Macartney-Christopher/5-Axis-Camera-Position-Control/Step Files/Focus & Zoom Extension/Small Lens Double Motor Platform.STEP

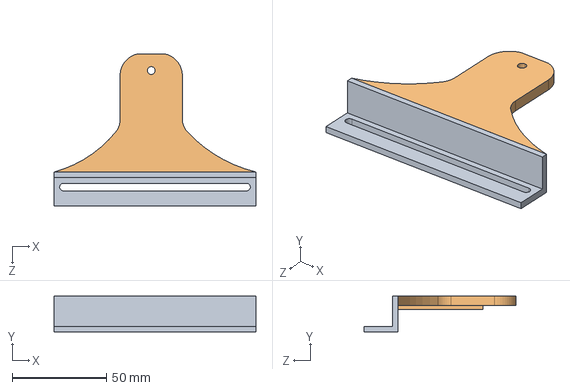
[picture p15: CAD file, 2021-04-19]
Step Files/Focus & Zoom Extension/Small Lens Double Motor Platform.STEP
107.0 x 19.0 x 80.5 mm
