Macartney-Christopher/5-Axis-Camera-Position-Control/Step Files/Tilt Hall Effect and Stepper Mount.STEP

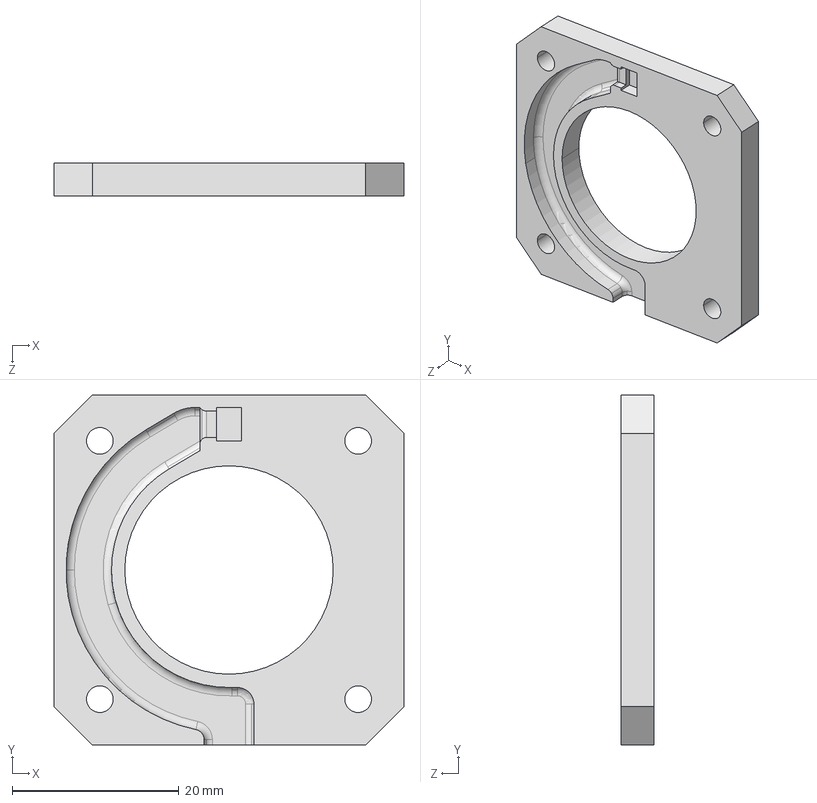
[picture p16: CAD file, 2021-03-15]
Step Files/Tilt Hall Effect and Stepper Mount.STEP
42.0 x 42.0 x 4.00 mm
