Macartney-Christopher/5-Axis-Camera-Position-Control/Step Files/Belt Clamp Lever.STEP

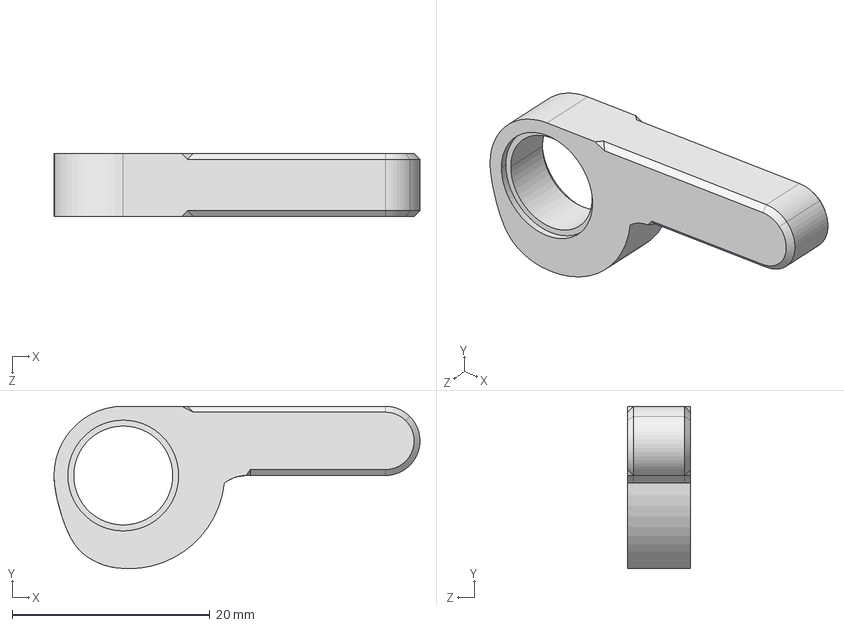
[picture p17: CAD file, 2021-03-15]
Step Files/Belt Clamp Lever.STEP
37.0 x 16.4 x 6.40 mm
