Macartney-Christopher/5-Axis-Camera-Position-Control/Step Files/Dynamic Lighting/Tripod Mount.STEP

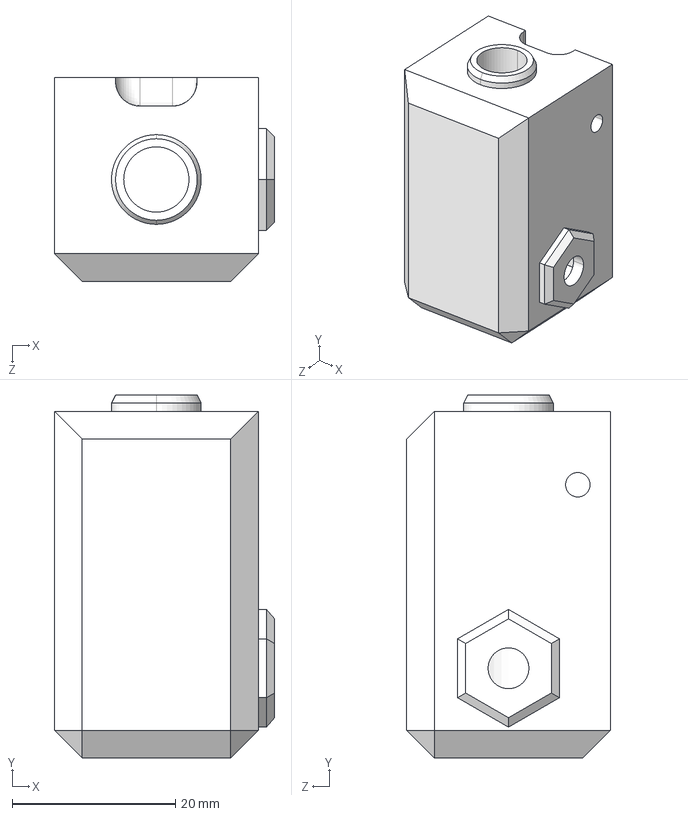
[picture p18: CAD file, 2021-04-19]
Step Files/Dynamic Lighting/Tripod Mount.STEP
27.0 x 44.5 x 25.0 mm
