Macartney-Christopher/5-Axis-Camera-Position-Control/Step Files/Focus & Zoom Extension/Tilt Camera Mount.STEP

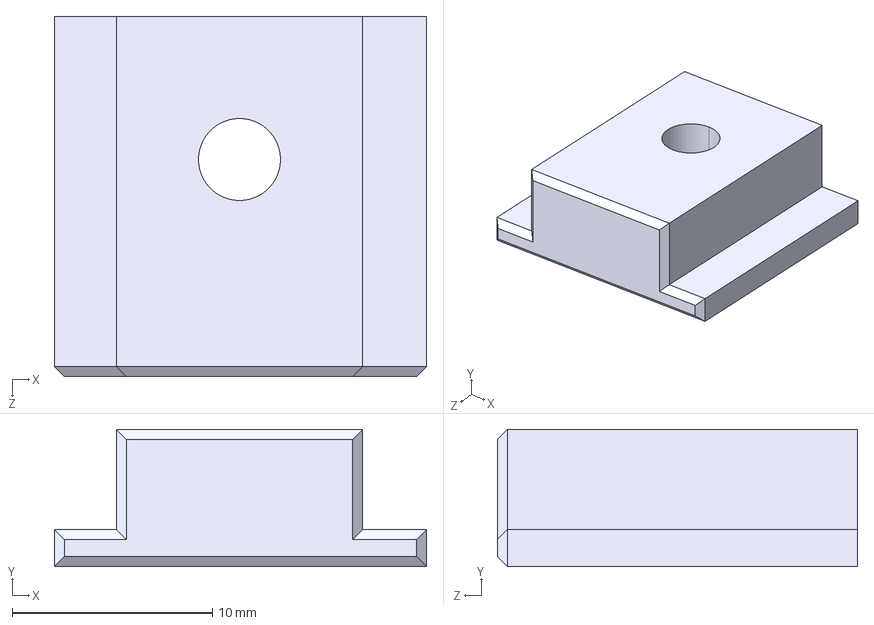
[picture p19: CAD file, 2021-04-19]
Step Files/Focus & Zoom Extension/Tilt Camera Mount.STEP
18.6 x 6.85 x 18.0 mm
