Macartney-Christopher/5-Axis-Camera-Position-Control/Step Files/Bearing Outter Race - 127 x 146.05 x 12.7mm.STEP

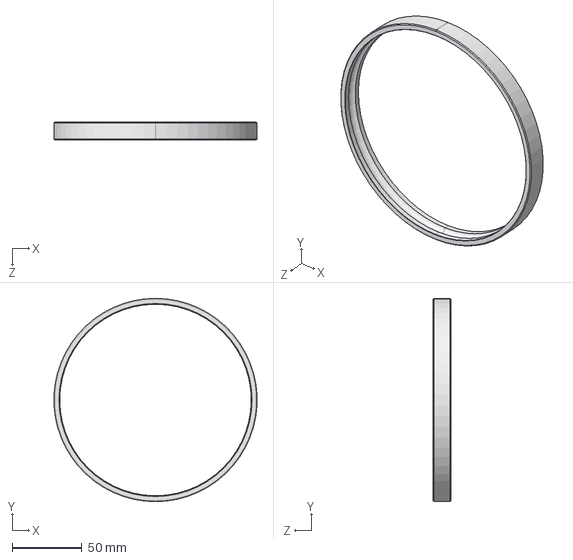
[picture p20: CAD file, 2021-03-15]
Step Files/Bearing Outter Race - 127 x 146.05 x 12.7mm.STEP
145.8 x 146.0 x 12.7 mm
