Macartney-Christopher/5-Axis-Camera-Position-Control/Step Files/Tilt Side Support - Idle.STEP

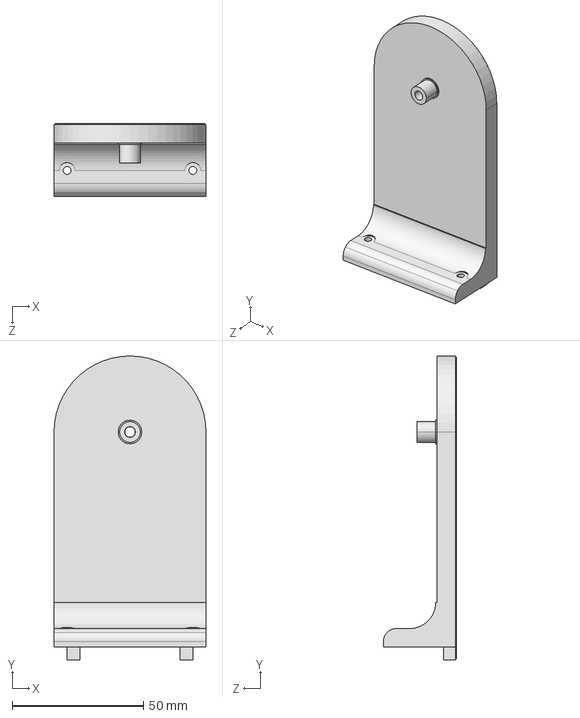
[picture p21: CAD file, 2021-03-15]
Step Files/Tilt Side Support - Idle.STEP
58.0 x 116.0 x 28.0 mm
