Macartney-Christopher/5-Axis-Camera-Position-Control/Step Files/Bearing Clip Ring.STEP

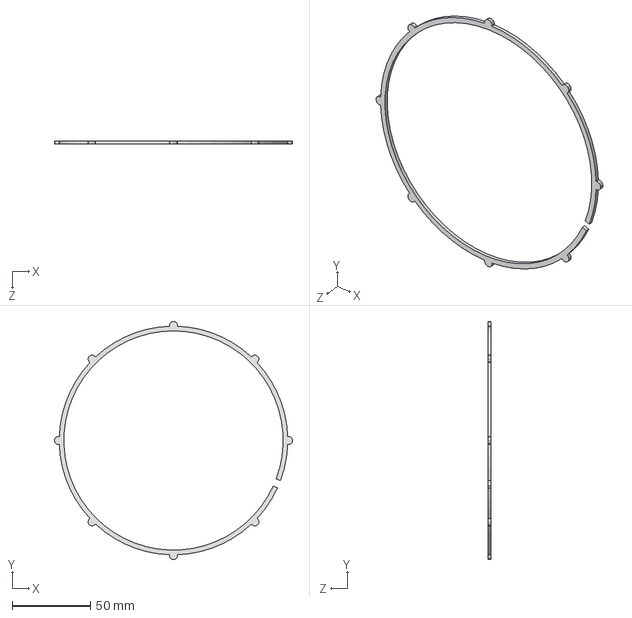
[picture p22: CAD file, 2021-03-15]
Step Files/Bearing Clip Ring.STEP
152.0 x 152.0 x 2.00 mm
