Macartney-Christopher/5-Axis-Camera-Position-Control/Step Files/Panning Platform.STEP

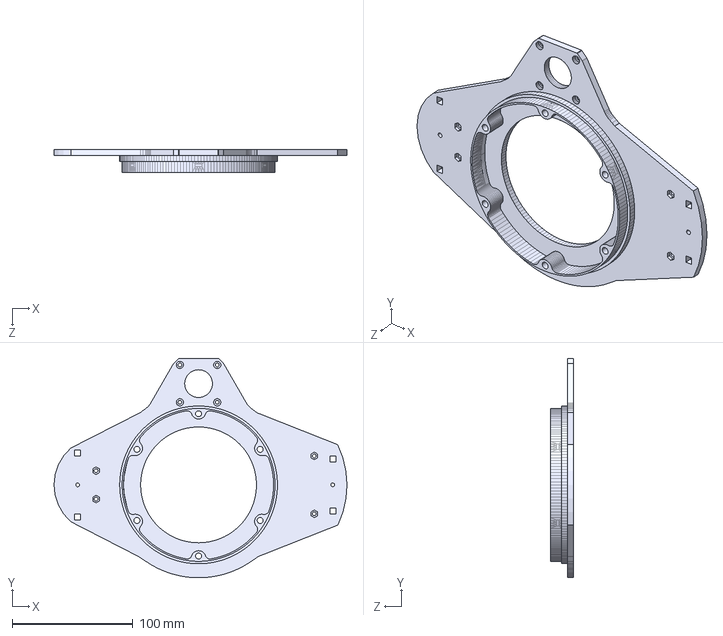
[picture p23: CAD file, 2021-03-15]
Step Files/Panning Platform.STEP
243.0 x 182.0 x 18.8 mm
