Macartney-Christopher/5-Axis-Camera-Position-Control/Step Files/Tilt - 21 Tooth Herringbone Gear Flexi.STEP

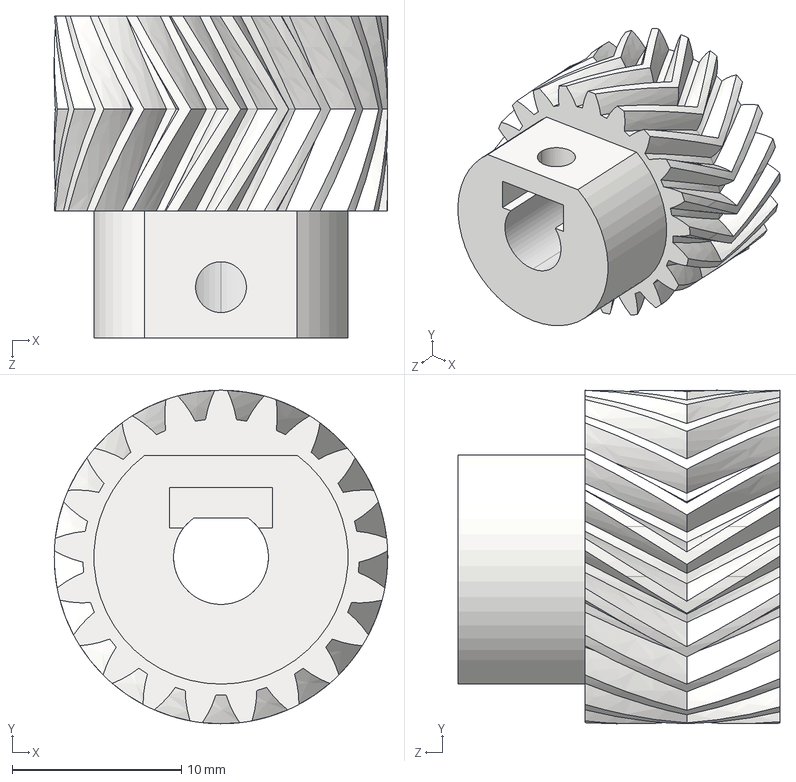
[picture p24: CAD file, 2021-03-15]
Step Files/Tilt - 21 Tooth Herringbone Gear Flexi.STEP
19.7 x 19.7 x 19.0 mm
