Macartney-Christopher/5-Axis-Camera-Position-Control/Step Files/2040 Hall Effect Support.STEP

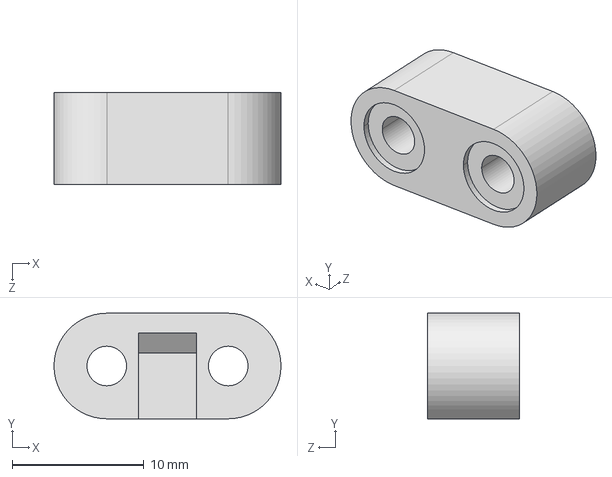
[picture p25: CAD file, 2021-03-15]
Step Files/2040 Hall Effect Support.STEP
17.2 x 8.00 x 7.00 mm
