Macartney-Christopher/5-Axis-Camera-Position-Control/Step Files/2040 Slider bottom.STEP

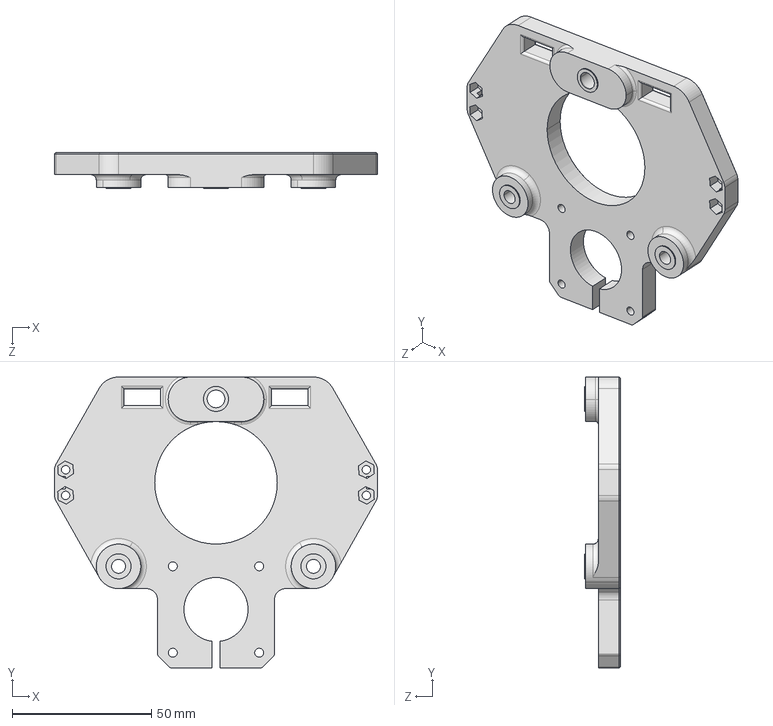
[picture p26: CAD file, 2021-03-15]
Step Files/2040 Slider bottom.STEP
116.0 x 104.5 x 13.0 mm
