Macartney-Christopher/5-Axis-Camera-Position-Control/Step Files/Bearing Middle Cage - 127 x 146.05 x 12.7mm.STEP

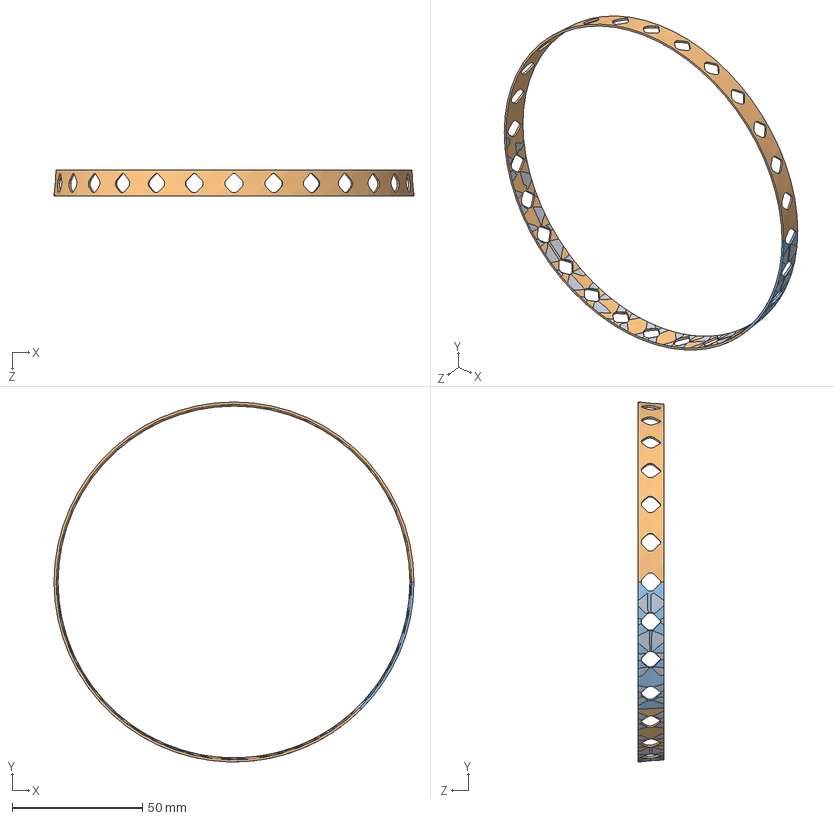
[picture p27: CAD file, 2021-03-15]
Step Files/Bearing Middle Cage - 127 x 146.05 x 12.7mm.STEP
138.1 x 138.1 x 9.90 mm
