Macartney-Christopher/5-Axis-Camera-Position-Control/Step Files/Tilt Camera Mount.STEP

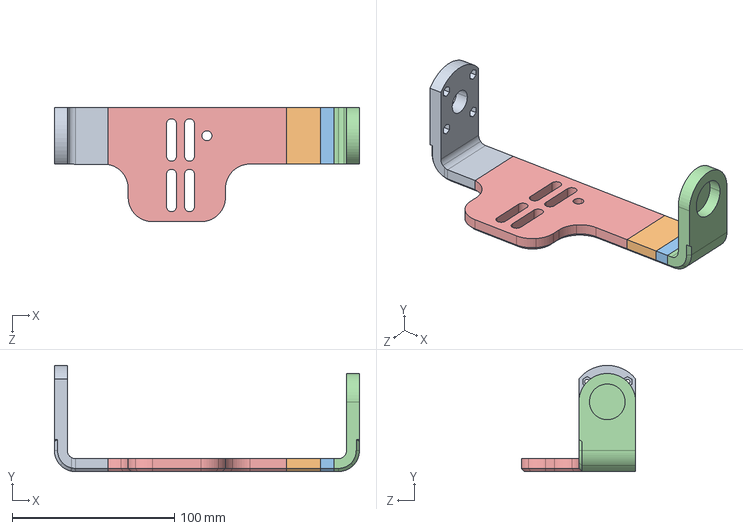
[picture p28: CAD file, 2021-03-15]
Step Files/Tilt Camera Mount.STEP
188.0 x 65.5 x 70.5 mm
