Macartney-Christopher/5-Axis-Camera-Position-Control/Step Files/2040 Slider top.STEP

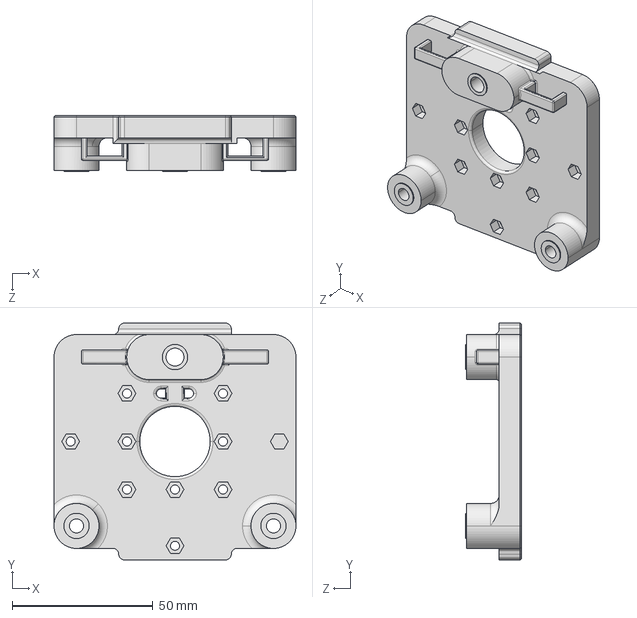
[picture p29: CAD file, 2021-03-15]
Step Files/2040 Slider top.STEP
86.0 x 84.1 x 20.0 mm
