Macartney-Christopher/5-Axis-Camera-Position-Control/Step Files/V-Slot Wheel Eccentric Spacer.STEP

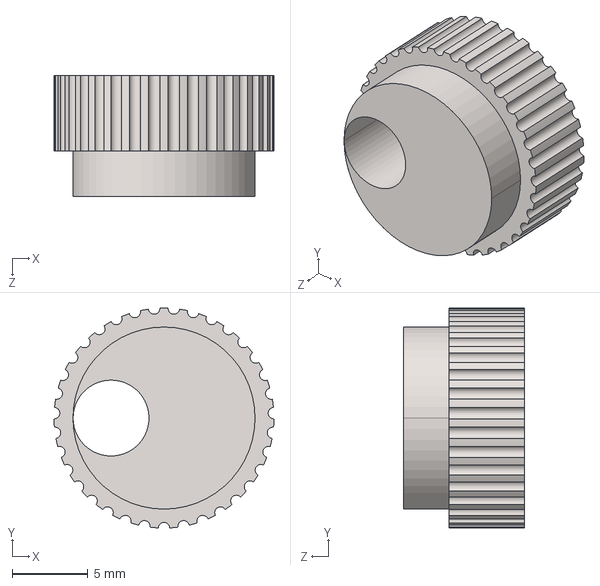
[picture p30: CAD file, 2021-03-15]
Step Files/V-Slot Wheel Eccentric Spacer.STEP
14.5 x 14.5 x 8.00 mm
