Macartney-Christopher/5-Axis-Camera-Position-Control/Step Files/Panning Hall Sensor Mount.STEP

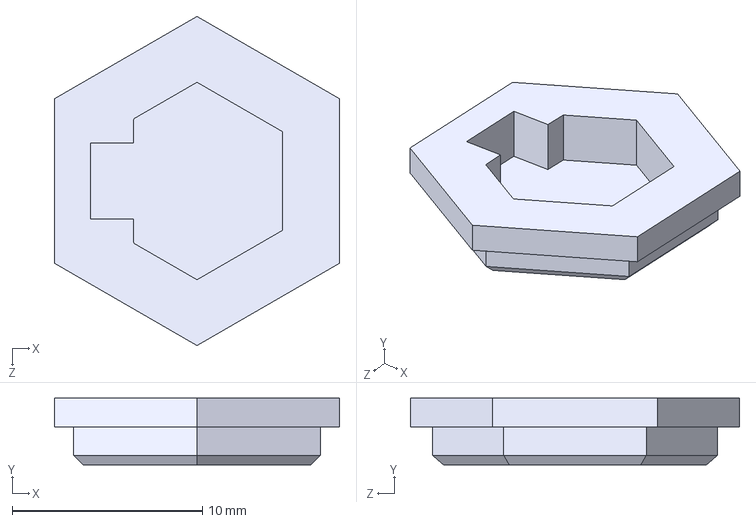
[picture p31: CAD file, 2021-03-15]
Step Files/Panning Hall Sensor Mount.STEP
15.0 x 3.50 x 17.3 mm
