Macartney-Christopher/5-Axis-Camera-Position-Control/Step Files/Panning - 17 Tooth Herringbone Gear.STEP

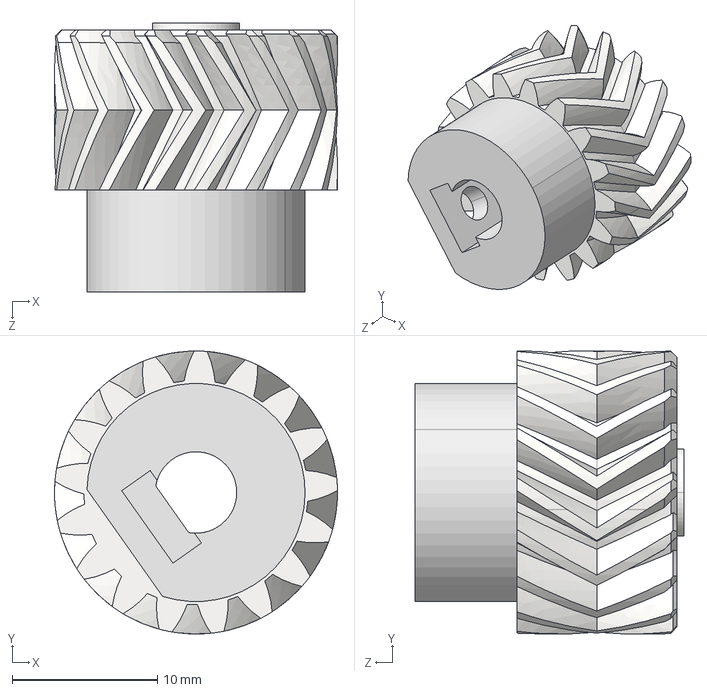
[picture p32: CAD file, 2021-03-15]
Step Files/Panning - 17 Tooth Herringbone Gear.STEP
19.5 x 19.5 x 18.5 mm
