Macartney-Christopher/5-Axis-Camera-Position-Control/Step Files/Tilt -  64 Tooth Herringbone Gear.STEP

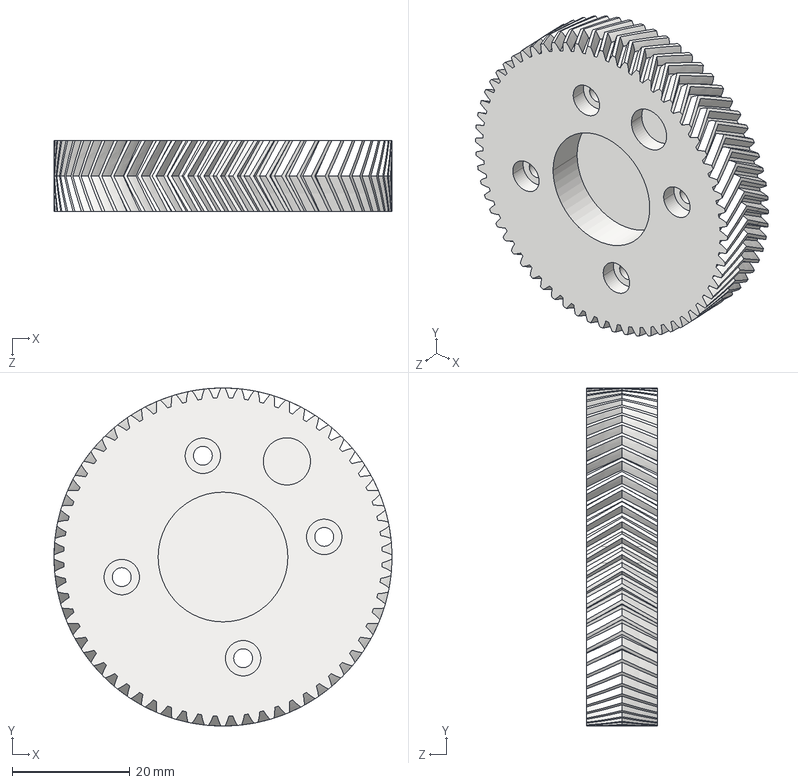
[picture p33: CAD file, 2021-03-15]
Step Files/Tilt - 64 Tooth Herringbone Gear.STEP
57.3 x 57.3 x 12.0 mm
