Macartney-Christopher/5-Axis-Camera-Position-Control/Step Files/Bearing Inner Race - 127 x 146.05 x 12.7mm.STEP

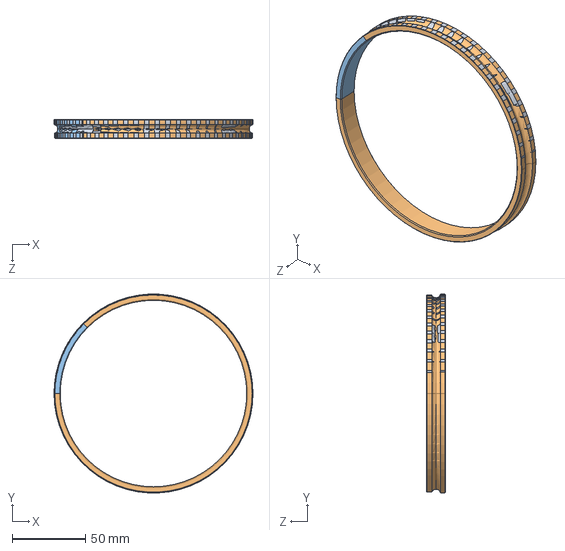
[picture p34: CAD file, 2021-03-15]
Step Files/Bearing Inner Race - 127 x 146.05 x 12.7mm.STEP
135.5 x 135.4 x 12.7 mm
