Macartney-Christopher/5-Axis-Camera-Position-Control/FlashStorage_PanTiltMount/panTiltMount.cpp

#include "PanTiltMount.h"
#include "PTM.h" //A library I created for Arduino that contains some simple functions I commonly use. Library available at: https://github.com/isaac879/Iibrary
#include <AccelStepper.h> //Library to control the stepper motors http://www.airspayce.com/mikem/arduino/AccelStepper/index.html
#include <MultiStepper.h> //Library to control multiple coordinated stepper motors http://www.airspayce.com/mikem/arduino/AccelStepper/classMultiStepper.html#details
#include "FlashStorage.h" //To be able to save values when powered off instead of EEPROM because Arduino Nano 33 BLE has more memory but no EEPROM

/*--------------------------------------------------------------------------------------------------------------------------------------------------------*/

//Global scope
AccelStepper stepper_pan = AccelStepper(1, PIN_STEP_PAN, PIN_DIRECTION_PAN);
AccelStepper stepper_tilt = AccelStepper(1, PIN_STEP_TILT, PIN_DIRECTION_TILT);
AccelStepper stepper_slider = AccelStepper(1, PIN_STEP_SLIDER, PIN_DIRECTION_SLIDER);
AccelStepper stepper_focus = AccelStepper(8, motorPin11, motorPin13, motorPin12, motorPin14);
AccelStepper stepper_zoom = AccelStepper(8, motorPin21, motorPin23, motorPin22, motorPin24);

MultiStepper multi_stepper;

KeyframeElement keyframe_array[KEYFRAME_ARRAY_LENGTH];

FlashStorage(homing_mode_store, byte);
FlashStorage(step_mode_store, int);
FlashStorage(pan_max_speed_store, float);
FlashStorage(tilt_max_speed_store, float);
FlashStorage(slider_max_speed_store, float);
FlashStorage(focus_max_speed_store, float);
FlashStorage(zoom_max_speed_store, float);
FlashStorage(hall_pan_offset_degrees_store, float);
FlashStorage(hall_tilt_offset_degrees_store, float);
FlashStorage(invert_pan_store, byte);
FlashStorage(invert_tilt_store, byte);
FlashStorage(invert_slider_store, byte);
FlashStorage(invert_focus_store, byte);
FlashStorage(invert_zoom_store, byte);
FlashStorage(degrees_per_picture_store, float);
FlashStorage(delay_ms_between_pictures_store, unsigned long);
FlashStorage(acceleration_enable_state_store, byte);
FlashStorage(pan_accel_increment_us_store, int);
FlashStorage(tilt_accel_increment_us_store, int);
FlashStorage(slider_accel_increment_us_store, int);
FlashStorage(focus_accel_increment_us_store, int);
FlashStorage(zoom_accel_increment_us_store, int);

int keyframe_elements = 0;
int current_keyframe_index = -1;
char stringText[MAX_STRING_LENGTH + 1];
float pan_steps_per_degree =(200.0 * SIXTEENTH_STEP * PAN_GEAR_RATIO) / 360.0; //Stepper motor has 200 steps per 360 degrees
float tilt_steps_per_degree = (200.0 * SIXTEENTH_STEP * TILT_GEAR_RATIO) / 360.0; //Stepper motor has 200 steps per 360 degrees
float slider_steps_per_millimetre = (200.0 * SIXTEENTH_STEP) / (SLIDER_PULLEY_TEETH * 2); //Stepper motor has 200 steps per 360 degrees, the timing pully has 36 teeth and the belt has a pitch of 2mm
float focus_steps_per_degree = ((2048.0 * SIXTEENTH_STEP * FOCUS_GEAR_RATIO) / 360.0); //this value was inputted manually to allow for more dynamic memory
float zoom_steps_per_degree = ((2048.0 * SIXTEENTH_STEP * ZOOM_GEAR_RATIO) / 360.0); // this value was inputted manually to allow for more dynamic memory

int step_mode = SIXTEENTH_STEP;
bool enable_state = true; //Stepper motor driver enable state
float hall_pan_offset_degrees = 0; //Offset to make the pan axis home position centred. This is required because the Hall sensor triggers before being centred on the magnet.
float hall_tilt_offset_degrees = 0; //Offset to make the tilt axis home position centred. This is required because the Hall sensor triggers before being centred on the magnet.
byte invert_pan = 0; //Variables to invert the direction of the axis. Note: These value gets set from the saved EEPROM value on startup. 
byte invert_tilt = 0;
byte invert_slider = 0;
byte invert_focus = 0;
byte invert_zoom = 0;
byte homing_mode = 0; //Note: Gets set from the saved EEPROM value on startup 
float pan_max_speed = 18; //degrees/second. Note: Gets set from the saved EEPROM value on startup. 
float tilt_max_speed = 10; //degrees/second.
float slider_max_speed = 20; //mm/second
float focus_max_speed = 10;
float zoom_max_speed = 10;

long target_position[5];//Array to store stepper motor step counts

float degrees_per_picture = 0.5; //Note: Gets set from the saved EEPROM value on startup. 
unsigned long delay_ms_between_pictures = 1000; //Note: Gets set from the saved EEPROM value on startup. 
int pan_accel_increment_us = 4000;
int tilt_accel_increment_us = 3000; 
int slider_accel_increment_us = 3500; 
int focus_accel_increment_us = 3000;
int zoom_accel_increment_us = 3000;

byte acceleration_enable_state = 0;
FloatCoordinate intercept;

/*--------------------------------------------------------------------------------------------------------------------------------------------------------*/

void initPanTilt(void){
    Serial.begin(BAUD_RATE);
    pinMode(PIN_MS1, OUTPUT);
    pinMode(PIN_MS2, OUTPUT);
    pinMode(PIN_ENABLE, OUTPUT);
    pinMode(PIN_DIRECTION_PAN, OUTPUT);
    pinMode(PIN_STEP_PAN, OUTPUT);
    pinMode(PIN_DIRECTION_TILT, OUTPUT);
    pinMode(PIN_STEP_TILT, OUTPUT);
    pinMode(PIN_DIRECTION_SLIDER, OUTPUT);
    pinMode(PIN_STEP_SLIDER, OUTPUT);
    pinMode(PIN_PAN_HALL, INPUT_PULLUP);
    pinMode(PIN_TILT_HALL, INPUT_PULLUP);
    pinMode(PIN_SLIDER_HALL, INPUT_PULLUP);
    pinMode(PIN_SHUTTER_TRIGGER, OUTPUT);
    digitalWrite(PIN_SHUTTER_TRIGGER, LOW);
    
    pinMode(motorPin11, OUTPUT);
    pinMode(motorPin12, OUTPUT);
    pinMode(motorPin13, OUTPUT);
    pinMode(motorPin14, OUTPUT);
    pinMode(motorPin21, OUTPUT);
    pinMode(motorPin22, OUTPUT);
    pinMode(motorPin23, OUTPUT);
    pinMode(motorPin24, OUTPUT);
    
    setStepMode(step_mode); //steping mode
    stepper_pan.setMaxSpeed(panDegreesToSteps(pan_max_speed));
    stepper_tilt.setMaxSpeed(tiltDegreesToSteps(tilt_max_speed));
    stepper_slider.setMaxSpeed(sliderMillimetresToSteps(slider_max_speed));

    stepper_focus.setMaxSpeed(1000); 
    stepper_zoom.setMaxSpeed(1000);
    
    stepper_pan.setAcceleration(5000);
    stepper_tilt.setAcceleration(5000);
    stepper_slider.setAcceleration(5000);
    
    stepper_focus.setAcceleration(5000);
    stepper_zoom.setAcceleration(5000);
    
    invertPanDirection(invert_pan);
    invertTiltDirection(invert_tilt);
    invertSliderDirection(invert_slider);

    multi_stepper.addStepper(stepper_pan);
    multi_stepper.addStepper(stepper_tilt);
    multi_stepper.addStepper(stepper_slider);

    multi_stepper.addStepper(stepper_focus);
    multi_stepper.addStepper(stepper_zoom);
    
    digitalWrite(PIN_ENABLE, LOW); //Enable the stepper drivers
}

/*--------------------------------------------------------------------------------------------------------------------------------------------------------*/

float boundFloat(float value, float lower, float upper){
    if(value < lower){
        value = lower;
    }
    else if(value > upper){
        value = upper;
    }
    return value;
}

/*--------------------------------------------------------------------------------------------------------------------------------------------------------*/

void serialFlush(void){
    while(Serial.available() > 0){
        char c = Serial.read();
    }
} 

/*--------------------------------------------------------------------------------------------------------------------------------------------------------*/

void enableSteppers(void){
    if(enable_state == false){
        digitalWrite(PIN_ENABLE, LOW); //Enable the stepper drivers
        enable_state = true;
        printi(F("Enabled\n"));
    }
    else{
        digitalWrite(PIN_ENABLE, HIGH); //Disabe the stepper drivers
        enable_state = false;
        printi(F("Disabled\n"));
    }
}

/*--------------------------------------------------------------------------------------------------------------------------------------------------------*/

void setStepMode(int newMode){ //Step modes for the TMC2208
    float stepRatio = (float)newMode / (float)step_mode; //Ratio between the new step mode and the previously set one. 
    if(newMode == HALF_STEP){
      digitalWrite(PIN_MS1, HIGH);
      digitalWrite(PIN_MS2, LOW);
        //PORTB |=   B00001000; //MS1 high
        //PORTB &= ~(B00000100); //MS2 low 
    }
    else if(newMode == QUARTER_STEP){
      digitalWrite(PIN_MS1, LOW);
      digitalWrite(PIN_MS2, HIGH);
        //PORTB |=   B00000100; //MS2 high
        //PORTB &= ~(B00001000); //MS1 low
    }
    else if(newMode == EIGHTH_STEP){
      digitalWrite(PIN_MS1, LOW);
      digitalWrite(PIN_MS2, LOW);
        //PORTB &= ~(B00001100); //MS1 and MS2 low
    }
    else if(newMode == SIXTEENTH_STEP){
      digitalWrite(PIN_MS1, HIGH);
      digitalWrite(PIN_MS2, HIGH);
        //PORTB |= B00001100; //MS1 and MS2 high
    }
    else{ //If an invalid step mode was entered.
        printi(F("Invalid mode. Enter 2, 4, 8 or 16\n"));
        return;
    }

 /* //Step modes for A4988
  * 
  * if(newMode == HALF_STEP){
      digitalWrite(PIN_MS1, HIGH);
      digitalWrite(PIN_MS2, LOW);
      digitalWrite(PIN_MS3, LOW);
    }
    else if(newMode == QUARTER_STEP){
        digitalWrite(PIN_MS1, LOW);
        digitalWrite(PIN_MS2, HIGH);
        digitalWrite(PIN_MS3, LOW);
    }
    else if(newMode == EIGHTH_STEP){
        digitalWrite(PIN_MS1, HIGH);
        digitalWrite(PIN_MS2, HIGH);
        digitalWrite(PIN_MS3, LOW);
    }
    else if(newMode == SIXTEENTH_STEP){
        digitalWrite(PIN_MS1, HIGH);
        digitalWrite(PIN_MS2, HIGH);
        digitalWrite(PIN_MS3, HIGH);
    }
    else{ //If an invalid step mode was entered.
        printi(F("Invalid mode. Enter 2, 4, 8 or 16\n"));
        return;
    }   
  * 
  * 
  * 
  * 
  * 
  * 
  */
    //Scale current step to match the new step mode
    stepper_pan.setCurrentPosition(stepper_pan.currentPosition() * stepRatio);
    stepper_tilt.setCurrentPosition(stepper_tilt.currentPosition() * stepRatio);
    stepper_slider.setCurrentPosition(stepper_slider.currentPosition() * stepRatio);

    stepper_focus.setCurrentPosition(stepper_focus.currentPosition() * stepRatio);
    stepper_zoom.setCurrentPosition(stepper_zoom.currentPosition() * stepRatio);

    pan_steps_per_degree = (200.0 * (float)newMode * PAN_GEAR_RATIO) / 360.0; //Stepper motor has 200 steps per 360 degrees
    tilt_steps_per_degree = (200.0 * (float)newMode * TILT_GEAR_RATIO) / 360.0; //Stepper motor has 200 steps per 360 degrees
    slider_steps_per_millimetre = (200.0 * (float)newMode) / (SLIDER_PULLEY_TEETH * 2.0); //Stepper motor has 200 steps per 360 degrees, the timing pully has 36 teeth and the belt has a pitch of 2mm
    
    focus_steps_per_degree = 9 * FOCUS_GEAR_RATIO *(2048 / 360); // 9 was determined through empirical testing
    zoom_steps_per_degree = 9 * ZOOM_GEAR_RATIO *(2048 / 360); // 9 was determined through empirical testing
    
    stepper_pan.setMaxSpeed(panDegreesToSteps(pan_max_speed));
    stepper_tilt.setMaxSpeed(tiltDegreesToSteps(tilt_max_speed));
    stepper_slider.setMaxSpeed(sliderMillimetresToSteps(slider_max_speed));
    
    stepper_focus.setMaxSpeed(1000); 
    stepper_zoom.setMaxSpeed(1000);

    step_mode = newMode;
    printi(F("Set to "), step_mode, F(" step mode.\n"));
    clearKeyframes();
}

/*--------------------------------------------------------------------------------------------------------------------------------------------------------*/

void panDegrees(float angle){
    target_position[0] = panDegreesToSteps(angle);
    if(acceleration_enable_state == 0){
        multi_stepper.moveTo(target_position);
    }
    else{
        stepper_pan.setCurrentPosition(stepper_pan.currentPosition());
        stepper_pan.runToNewPosition(panDegreesToSteps(angle));
    }    
}

/*--------------------------------------------------------------------------------------------------------------------------------------------------------*/

void tiltDegrees(float angle){
    target_position[1] = tiltDegreesToSteps(angle);
    if(acceleration_enable_state == 0){
        multi_stepper.moveTo(target_position);
    }
    else{
        stepper_tilt.setCurrentPosition(stepper_tilt.currentPosition());
        stepper_tilt.runToNewPosition(tiltDegreesToSteps(angle));
    }
}

/*--------------------------------------------------------------------------------------------------------------------------------------------------------*/

void focusDegrees(float angle){ 
    target_position[3] = focusDegreesToSteps(angle);
    if(acceleration_enable_state == 0){
        multi_stepper.moveTo(target_position);
    }
    else{
        stepper_tilt.setCurrentPosition(stepper_tilt.currentPosition());
        stepper_tilt.runToNewPosition(focusDegreesToSteps(angle));
    }
}

/*--------------------------------------------------------------------------------------------------------------------------------------------------------*/

void zoomDegrees(float angle){     
    target_position[4] = zoomDegreesToSteps(angle);
    if(acceleration_enable_state == 0){
        multi_stepper.moveTo(target_position);
    }
    else{
        stepper_tilt.setCurrentPosition(stepper_tilt.currentPosition());
        stepper_tilt.runToNewPosition(zoomDegreesToSteps(angle));
    }
} 

/*--------------------------------------------------------------------------------------------------------------------------------------------------------*/

float panDegreesToSteps(float angle){
    return pan_steps_per_degree * angle;
}

/*--------------------------------------------------------------------------------------------------------------------------------------------------------*/

float tiltDegreesToSteps(float angle){
    return tilt_steps_per_degree * angle;
}

/*--------------------------------------------------------------------------------------------------------------------------------------------------------*/

long sliderMillimetresToSteps(float mm){
    return round(mm * slider_steps_per_millimetre);
}

/*--------------------------------------------------------------------------------------------------------------------------------------------------------*/

float focusDegreesToSteps(float angle){
    return focus_steps_per_degree * angle;
}

/*--------------------------------------------------------------------------------------------------------------------------------------------------------*/

float zoomDegreesToSteps(float angle){
    return zoom_steps_per_degree * angle;
}

/*--------------------------------------------------------------------------------------------------------------------------------------------------------*/
float sliderStepsToMillimetres(long steps){
    return (float)steps / slider_steps_per_millimetre;
}

/*--------------------------------------------------------------------------------------------------------------------------------------------------------*/

void sliderMoveTo(float mm){
    target_position[2] = sliderMillimetresToSteps(mm);
    if(acceleration_enable_state == 0){ 
        multi_stepper.moveTo(target_position);
    }
    else{
        stepper_slider.setCurrentPosition(stepper_slider.currentPosition());
        stepper_slider.runToNewPosition(sliderMillimetresToSteps(mm));
    }    
}

/*--------------------------------------------------------------------------------------------------------------------------------------------------------*/

void printKeyframeElements(void){
    printi(F("Keyframe index: "), current_keyframe_index, F("\n"));
    for(int row = 0; row < keyframe_elements; row++){
        printi(F(""), row, F("\t|"));
        printi(F(" Pan: "), panStepsToDegrees(keyframe_array[row].panStepCount), 3, F("º\t"));
        printi(F("Tilt: "), tiltStepsToDegrees(keyframe_array[row].tiltStepCount), 3, F("º\t"));
        printi(F("Slider: "), sliderStepsToMillimetres(keyframe_array[row].sliderStepCount), 3, F("mm\t"));
        printi(F("Zoom: "), zoomStepsToDegrees(keyframe_array[row].zoomStepCount), 3, F("º\t"));
        printi(F("Focus: "), focusStepsToDegrees(keyframe_array[row].focusStepCount), 3, F("º\t"));
        printi(F("Pan Speed: "), panStepsToDegrees(keyframe_array[row].panSpeed), 3, F(" º/s\t"));
        printi(F("Tilt Speed: "), tiltStepsToDegrees(keyframe_array[row].tiltSpeed), 3, F(" º/s\t"));  
        printi(F("Slider Speed: "), sliderStepsToMillimetres(keyframe_array[row].sliderSpeed), 3, F(" mm/s\t"));      
        printi(F("Delay: "), keyframe_array[row].msDelay, F("ms |\n"));    
    }
    printi(F("\n"));
}

/*--------------------------------------------------------------------------------------------------------------------------------------------------------*/

void debugReport(void){
    printi(F("Status\n"));
    printi(F("Status\nEnable state: "), enable_state);
    printi(F("Step Mode: "), step_mode);
    printi(F("Pan angle: "), panStepsToDegrees(stepper_pan.currentPosition()), 3, F("º\n"));
    printi(F("Tilt angle: "), tiltStepsToDegrees(stepper_tilt.currentPosition()), 3, F("º\n")); 
    printi(F("Slider position: "), sliderStepsToMillimetres(stepper_slider.currentPosition()), 3, F("mm\n"));  
    printi(F("Pan max steps/s: "), stepper_pan.maxSpeed());
    printi(F("Tilt max steps/s: "), stepper_tilt.maxSpeed());
    printi(F("Slider max steps/s: "), stepper_slider.maxSpeed());
    printi(F("Pan max speed: "), panStepsToDegrees(stepper_pan.maxSpeed()), 3, F("º/s\n"));
    printi(F("Tilt max speed: "), tiltStepsToDegrees(stepper_tilt.maxSpeed()), 3, F("º/s\n"));
    printi(F("Slider max speed: "), sliderStepsToMillimetres(stepper_slider.maxSpeed()), 3, F("mm/s\n"));        
    //printi(F("Battery: "), getBatteryPercentage(), 3, F("%\n"));
    printi(F("Battery: "), getBatteryVoltage(), 3, F("V\n"));
    printi(F("Homing mode: "), homing_mode);    
    printi(F("Angle between pics: "), degrees_per_picture, 3, F("º\n"));
    printi(F("Panoramiclapse delay between pics: "), delay_ms_between_pictures, F("ms\n"));   
    printi(F(VERSION_NUMBER));
    printEEPROM();
    printKeyframeElements();
    printi(F("\n"));
}

/*--------------------------------------------------------------------------------------------------------------------------------------------------------*/

void setTargetPositions(float panDeg, float tiltDeg, float sliderMillimetre, float focusDeg,float zoomDeg ){
    target_position[0] = panDegreesToSteps(panDeg);
    target_position[1] = tiltDegreesToSteps(tiltDeg);
    target_position[2] = sliderMillimetresToSteps(sliderMillimetre);

    target_position[3] = focusDegreesToSteps(focusDeg);
    target_position[4] = zoomDegreesToSteps(zoomDeg);
    
    multi_stepper.moveTo(target_position); 
}
/*--------------------------------------------------------------------------------------------------------------------------------------------------------*/

bool findHome(void){
    bool panHomeFlag = false;
    bool tiltHomeFlag = false;
    bool sliderHomeFlag = false;
    int panHomingDir = -1;
    int tiltHomingDir = -1; 
      
    target_position[0] = stepper_pan.currentPosition();
    target_position[1] = stepper_tilt.currentPosition();
    target_position[2] = stepper_slider.currentPosition();
    
    if(homing_mode == 0){ //No homing
        return false;  
    }
    
    if(homing_mode == 1 || homing_mode == 3){ //Home the slider
        while(digitalRead(PIN_SLIDER_HALL) == 0){ //Move off the hall
            target_position[2] = target_position[2] + sliderMillimetresToSteps(0.1); 
            multi_stepper.moveTo(target_position); 
            multi_stepper.runSpeedToPosition();        
        }
        setTargetPositions(panStepsToDegrees(target_position[0]), tiltStepsToDegrees(target_position[1]), -1000,0,0);//1200 is about the length of the slider
        while(multi_stepper.run()){
            if(digitalRead(PIN_SLIDER_HALL) == 0){
                stepper_slider.setCurrentPosition(0);//set step count to 0
                setTargetPositions(panStepsToDegrees(target_position[0]), tiltStepsToDegrees(target_position[1]), 0,0,0);
                sliderHomeFlag = true;
            }
        }
    }

    long sliderPos = sliderStepsToMillimetres(stepper_slider.currentPosition());
    
    if(homing_mode == 2 || homing_mode == 3){ //Home pan and tilt
        while(digitalRead(PIN_PAN_HALL) == 0 || digitalRead(PIN_TILT_HALL) == 0){//If already on a Hall sensor move off
            target_position[0] = target_position[0] + panDegreesToSteps(!digitalRead(PIN_PAN_HALL));//increment by 1 degree
            target_position[1] = target_position[1] + tiltDegreesToSteps(!digitalRead(PIN_TILT_HALL));//increment by 1 degree
            if(target_position[0] > panDegreesToSteps(360) && target_position[1] > tiltDegreesToSteps(360)){//If both axis have done more than a full rotation there must be an issue...
                return false;
            }
            multi_stepper.moveTo(target_position); 
            multi_stepper.runSpeedToPosition();
        }
        stepper_pan.setCurrentPosition(0);//set step count to 0
        stepper_tilt.setCurrentPosition(0);//set step count to 0
    
        setTargetPositions(-45, -45, sliderPos,0,0);
        while(multi_stepper.run()){
            if(digitalRead(PIN_PAN_HALL) == 0){
                stepper_pan.setCurrentPosition(0);//set step count to 0
                setTargetPositions(0, -45 * !tiltHomeFlag, sliderPos,0,0);
                panHomeFlag = true;
                panHomingDir = 1;
            }
            if(digitalRead(PIN_TILT_HALL) == 0){
                stepper_tilt.setCurrentPosition(0);
                setTargetPositions(-45 * !panHomeFlag, 0, sliderPos,0,0);
                tiltHomeFlag = true;
                tiltHomingDir = 1;
            }
        }     
        
        setTargetPositions(360 * !panHomeFlag, 360 * !tiltHomeFlag, sliderPos,0,0);//full rotation on both axis so it must pass the home position
        while(multi_stepper.run()){
            if(digitalRead(PIN_PAN_HALL) == 0){
                stepper_pan.setCurrentPosition(0);//set step count to 0
                setTargetPositions(0, 360 * !tiltHomeFlag, sliderPos,0,0);
                panHomeFlag = true;
            }
            if(digitalRead(PIN_TILT_HALL)  == 0){
                stepper_tilt.setCurrentPosition(0);
                setTargetPositions(360 * !panHomeFlag, 0, sliderPos,0,0);
                tiltHomeFlag = true;
            }
        } 
    }
    
    if(panHomeFlag && tiltHomeFlag && (homing_mode == 2 || homing_mode == 3)){
        setTargetPositions(hall_pan_offset_degrees * panHomingDir, hall_tilt_offset_degrees * tiltHomingDir, sliderPos,0,0);
        multi_stepper.runSpeedToPosition();
        stepper_pan.setCurrentPosition(0);//set step count to 0
        stepper_tilt.setCurrentPosition(0);//set step count to 0
        setTargetPositions(0, 0, sliderPos,0,0);
        if(homing_mode == 3 && sliderHomeFlag == false){
            return false;
        }
        else{
            return true;
        }
    }
    else if(sliderHomeFlag){
        return true;
    }
    else{
        return false;
    }
}

/*--------------------------------------------------------------------------------------------------------------------------------------------------------*/

float getBatteryVoltage(void){ //TODO: Calibrate the values for your battery
    return mapNumber(analogRead(PIN_INPUT_VOLTAGE), 0, 1007, 0, 12.6);//1007 = 12.6V
}

/*--------------------------------------------------------------------------------------------------------------------------------------------------------*/

float getBatteryPercentage(void){ //TODO: Calibrate the values for your battery
    return boundFloat(mapNumber(getBatteryVoltage(), 9, 12.6, 0, 100), 0, 100); //780 = 9V = 0%, 1023 = 12.6V = 100%
}

/*--------------------------------------------------------------------------------------------------------------------------------------------------------*/

float panStepsToDegrees(long steps){
    return steps / pan_steps_per_degree;
}

/*--------------------------------------------------------------------------------------------------------------------------------------------------------*/

float panStepsToDegrees(float steps){
    return steps / pan_steps_per_degree;
}

/*--------------------------------------------------------------------------------------------------------------------------------------------------------*/

float tiltStepsToDegrees(long steps){
    return steps / tilt_steps_per_degree;
}

/*--------------------------------------------------------------------------------------------------------------------------------------------------------*/

float tiltStepsToDegrees(float steps){
    return steps / tilt_steps_per_degree;
}

/*--------------------------------------------------------------------------------------------------------------------------------------------------------*/
float zoomStepsToDegrees(long steps){
    return steps / zoom_steps_per_degree;
}

/*--------------------------------------------------------------------------------------------------------------------------------------------------------*/

float zoomStepsToDegrees(float steps){
    return steps / zoom_steps_per_degree;
}

/*--------------------------------------------------------------------------------------------------------------------------------------------------------*/
float focusStepsToDegrees(long steps){
    return steps / focus_steps_per_degree;
}

/*--------------------------------------------------------------------------------------------------------------------------------------------------------*/

float focusStepsToDegrees(float steps){
    return steps / focus_steps_per_degree;
}

/*--------------------------------------------------------------------------------------------------------------------------------------------------------*/

int addPosition(void){
    if(keyframe_elements >= 0 && keyframe_elements < KEYFRAME_ARRAY_LENGTH){
        keyframe_array[keyframe_elements].panStepCount = stepper_pan.currentPosition();
        keyframe_array[keyframe_elements].tiltStepCount = stepper_tilt.currentPosition();    
        keyframe_array[keyframe_elements].sliderStepCount = stepper_slider.currentPosition();
        
        keyframe_array[keyframe_elements].focusStepCount = stepper_focus.currentPosition();
        keyframe_array[keyframe_elements].zoomStepCount = stepper_zoom.currentPosition();
            
        keyframe_array[keyframe_elements].panSpeed = stepper_pan.maxSpeed();
        keyframe_array[keyframe_elements].tiltSpeed = stepper_tilt.maxSpeed();    
        keyframe_array[keyframe_elements].sliderSpeed = stepper_slider.maxSpeed();   

        keyframe_array[keyframe_elements].focusSpeed = stepper_focus.maxSpeed(); 
        keyframe_array[keyframe_elements].zoomSpeed = stepper_zoom.maxSpeed(); 
           
        keyframe_array[keyframe_elements].msDelay = 0;      
        current_keyframe_index = keyframe_elements;
        keyframe_elements++;//increment the index
        printi(F("Added at index: "), current_keyframe_index);
        return 0;
    }
    else{
        printi(F("Max number of keyframes reached\n"));
    }
    return -1;
}

/*--------------------------------------------------------------------------------------------------------------------------------------------------------*/

void clearKeyframes(void){
    keyframe_elements = 0;
    current_keyframe_index = -1;
    printi(F("Keyframes cleared\n"));
}

/*--------------------------------------------------------------------------------------------------------------------------------------------------------*/

void moveToIndex(int index){
    if(index < keyframe_elements && index >= 0){
        target_position[0] = keyframe_array[index].panStepCount;
        target_position[1] = keyframe_array[index].tiltStepCount;
        target_position[2] = keyframe_array[index].sliderStepCount;
        
        target_position[3] = keyframe_array[index].focusStepCount;
        target_position[4] = keyframe_array[index].zoomStepCount;
        
        stepper_pan.setMaxSpeed(keyframe_array[index].panSpeed);
        stepper_tilt.setMaxSpeed(keyframe_array[index].tiltSpeed);
        stepper_slider.setMaxSpeed(keyframe_array[index].sliderSpeed);

        stepper_focus.setMaxSpeed(keyframe_array[index].focusSpeed);
        stepper_zoom.setMaxSpeed(keyframe_array[index].zoomSpeed);

        if(acceleration_enable_state == 0){ //If accelerations are not enabled just move directly to the target position. 
            multi_stepper.moveTo(target_position); //Sets new target positions
            multi_stepper.runSpeedToPosition(); //Moves and blocks until complete
            delay(keyframe_array[index].msDelay);
            current_keyframe_index = index;
            return;
        }
        
        float panInitialSpeed = stepper_pan.speed();
        float tiltInitialSpeed = stepper_tilt.speed();
        float sliderInitialSpeed = stepper_slider.speed();
        
        float focusInitialSpeed = stepper_focus.speed();
        float zoomInitialSpeed = stepper_zoom.speed();

        if(index >= 1){
            if(keyframe_array[index - 1].msDelay != 0){
                panInitialSpeed = 0;
                tiltInitialSpeed = 0;
                sliderInitialSpeed = 0;
                
                focusInitialSpeed = 0;
                zoomInitialSpeed = 0;                
            }
        }
        
        multi_stepper.moveTo(target_position); //Sets new target positions //sets speeds

        float panDeltaSpeed = stepper_pan.speed() - panInitialSpeed;
        float tiltDeltaSpeed = stepper_tilt.speed() - tiltInitialSpeed;
        float sliderDeltaSpeed = stepper_slider.speed() - sliderInitialSpeed;
        
        float focusDeltaSpeed = stepper_focus.speed() - focusInitialSpeed;
        float zoomDeltaSpeed = stepper_zoom.speed() - zoomInitialSpeed;
        
        float panAccel = stepper_pan.speed() / (pan_accel_increment_us * 0.0001); //Equation is arbitrary and was determined through empirical testing. The acceleration value does NOT correspond to mm/s/s
        float tiltAccel = stepper_tilt.speed() / (tilt_accel_increment_us * 0.0001);
        float sliderAccel = stepper_slider.speed() / (slider_accel_increment_us * 0.0001); 
        
        long panDist = 0;
        long tiltDist = 0;
        long sliderDist = 0;
        long focusDist = 0;
        long zoomDist = 0;
        
        if(panAccel != 0){
            panDist = pow(stepper_pan.speed(), 2) / (5 * panAccel); //Equation is arbitrary and was deterined through empirical testing.
        }
        if(tiltAccel != 0){
            tiltDist = pow(stepper_tilt.speed(), 2) / (5 * tiltAccel); //Equation is arbitrary and was deterined through empirical testing.
        }
        if(sliderAccel != 0){
            sliderDist = pow(stepper_slider.speed(), 2) / (5 * sliderAccel); //Equation is arbitrary and was deterined through empirical testing.
        }

        if(index + 1 < keyframe_elements){//makes sure there is a valid next keyframe
            if(keyframe_array[index].msDelay == 0){
                long panStepDiff = keyframe_array[index + 1].panStepCount - keyframe_array[index].panStepCount; //Change in position from current target position to the next.
                long tiltStepDiff = keyframe_array[index + 1].tiltStepCount - keyframe_array[index].tiltStepCount;
                long sliderStepDiff = keyframe_array[index + 1].sliderStepCount - keyframe_array[index].sliderStepCount;

                long focusStepDiff = keyframe_array[index + 1].focusStepCount - keyframe_array[index].focusStepCount;
                long zoomStepDiff = keyframe_array[index + 1].zoomStepCount - keyframe_array[index].zoomStepCount;
                
                if((panStepDiff == 0 && stepper_pan.speed() != 0) || (panStepDiff > 0 && stepper_pan.speed() < 0) || (panStepDiff < 0 && stepper_pan.speed() > 0)){ //if stopping or changing direction
                    target_position[0] = keyframe_array[index].panStepCount - panDist; //Set the target position slightly before the actual target to allow for the distance traveled while decelerating.
                }
                if((tiltStepDiff == 0 && stepper_tilt.speed() != 0) || (tiltStepDiff > 0 && stepper_tilt.speed() < 0) || (tiltStepDiff < 0 && stepper_tilt.speed() > 0)){ //if stopping or changing direction
                    target_position[1] = keyframe_array[index].tiltStepCount - tiltDist;
                }
                if((sliderStepDiff == 0 && stepper_slider.speed() != 0) || (sliderStepDiff > 0 && stepper_slider.speed() < 0) || (sliderStepDiff < 0 && stepper_slider.speed() > 0)){ //if stopping or changing direction
                    target_position[2] = keyframe_array[index].sliderStepCount - sliderDist;//If changing dir
                }
                if((focusStepDiff == 0 && stepper_focus.speed() != 0) || (focusStepDiff > 0 && stepper_focus.speed() < 0) || (focusStepDiff < 0 && stepper_focus.speed() > 0)){ //if stopping or changing direction
                    target_position[3] = keyframe_array[index].focusStepCount - focusDist;//If changing dir
                }
                if((zoomStepDiff == 0 && stepper_zoom.speed() != 0) || (zoomStepDiff > 0 && stepper_zoom.speed() < 0) || (zoomStepDiff < 0 && stepper_zoom.speed() > 0)){ //if stopping or changing direction
                    target_position[4] = keyframe_array[index].zoomStepCount - zoomDist;//If changing dir
                }
            }
        }

        if(index > 0){
            long panStepDiffPrev = keyframe_array[index].panStepCount - keyframe_array[index - 1].panStepCount; //Change in position from the previous target to the current target position.
            long tiltStepDiffPrev = keyframe_array[index].tiltStepCount - keyframe_array[index - 1].tiltStepCount;
            long sliderStepDiffPrev = keyframe_array[index].sliderStepCount - keyframe_array[index - 1].sliderStepCount;

            long focusStepDiffPrev = keyframe_array[index].focusStepCount - keyframe_array[index - 1].focusStepCount;
            long zoomStepDiffPrev = keyframe_array[index].zoomStepCount - keyframe_array[index - 1].zoomStepCount;
            
            if(panStepDiffPrev == 0 && panDeltaSpeed == 0){ //Movement stopping
                panDeltaSpeed = -(2 * stepper_pan.speed()); //Making it negative ramps the speed down in the acceleration portion of the movement. The multiplication factor is arbitrary and was deterined through empirical testing.
            }
            if(tiltStepDiffPrev == 0 && tiltDeltaSpeed == 0){ //Movement stopping
                tiltDeltaSpeed = -(2 * stepper_tilt.speed());
            }
            if(sliderStepDiffPrev == 0 && sliderDeltaSpeed == 0){ //Movement stopping
                sliderDeltaSpeed = -(2 * stepper_slider.speed());
            }
            if(focusStepDiffPrev == 0 && focusDeltaSpeed == 0){ //Movement stopping
                focusDeltaSpeed = -(2 * stepper_focus.speed());
            }
            if(zoomStepDiffPrev == 0 && zoomDeltaSpeed == 0){ //Movement stopping
                zoomDeltaSpeed = -(2 * stepper_zoom.speed());
            }
        }
        
        multi_stepper.moveTo(target_position); //Sets new target positions and calculates new speeds.
        
        if(stepper_pan.currentPosition() != target_position[0] || stepper_tilt.currentPosition() != target_position[1] || stepper_slider.currentPosition() != target_position[2]){ //Prevents issues caused when the motor target positions and speeds not being updated becuase they have not changed.
            //Impliments the acceleration/deceleration. This implimentation feels pretty bad and should probably be updated but it works well enough so I'm not going to...
            float panInc = 0;
            float tiltInc = 0;
            float sliderInc = 0;
            unsigned long pan_last_us = 0;
            unsigned long tilt_last_us = 0;
            unsigned long slider_last_us = 0;
            
            while(((panInc < 1) || (tiltInc < 1) || (sliderInc < 1)) && multi_stepper.run()){
                unsigned long usTime = micros();
                
                if(usTime - pan_accel_increment_us >= pan_last_us){
                    panInc = (panInc < 1) ? (panInc + 0.01) : 1;
                    pan_last_us = micros();
                    stepper_pan.setSpeed(panInitialSpeed + (panDeltaSpeed * panInc));
                }
                
                if(usTime - tilt_accel_increment_us >= tilt_last_us){
                    tiltInc = (tiltInc < 1) ? (tiltInc + 0.01) : 1;
                    tilt_last_us = micros();
                    stepper_tilt.setSpeed(tiltInitialSpeed + (tiltDeltaSpeed * tiltInc));
                }
                
                if(usTime - slider_accel_increment_us >= slider_last_us){
                    sliderInc = (sliderInc < 1) ? (sliderInc + 0.01) : 1;
                    slider_last_us = micros();
                    stepper_slider.setSpeed(sliderInitialSpeed + (sliderDeltaSpeed * sliderInc));
                }
            }

            multi_stepper.moveTo(target_position); //Sets all speeds to reach the target
            multi_stepper.runSpeedToPosition(); //Moves and blocks until complete
        }
        delay(keyframe_array[index].msDelay);
        current_keyframe_index = index;
    }
}

/*--------------------------------------------------------------------------------------------------------------------------------------------------------*/

void executeMoves(int repeat){
    stepper_pan.setSpeed(0);
    stepper_tilt.setSpeed(0);
    stepper_slider.setSpeed(0);
    stepper_focus.setSpeed(0);
    stepper_zoom.setSpeed(0);
    for(int i = 0; i < repeat; i++){
        for(int row = 0; row < keyframe_elements; row++){
            moveToIndex(row);
        }
//        if(getBatteryVoltage() < 9.5){//9.5V is used as the cut off to allow for inaccuracies and be on the safe side.
//            delay(200);
//            if(getBatteryVoltage() < 9.5){//Check voltage is still low and the first wasn't a miscellaneous reading
//                printi(F("Battery low"));
//                while(1){}//loop and do nothing
//            }
//        }
    }
}

/*--------------------------------------------------------------------------------------------------------------------------------------------------------*/

void gotoFirstKeyframe(void){
    moveToIndex(0);
}

/*--------------------------------------------------------------------------------------------------------------------------------------------------------*/

void gotoLastKeyframe(void){
    moveToIndex(keyframe_elements - 1);
}

/*--------------------------------------------------------------------------------------------------------------------------------------------------------*/

void editKeyframe(void){
    keyframe_array[current_keyframe_index].panStepCount = stepper_pan.currentPosition();
    keyframe_array[current_keyframe_index].tiltStepCount = stepper_tilt.currentPosition(); 
    keyframe_array[current_keyframe_index].sliderStepCount = stepper_slider.currentPosition(); 

    keyframe_array[current_keyframe_index].focusStepCount = stepper_focus.currentPosition(); 
    keyframe_array[current_keyframe_index].zoomStepCount = stepper_zoom.currentPosition();     
    
    keyframe_array[current_keyframe_index].panSpeed = stepper_pan.maxSpeed();
    keyframe_array[current_keyframe_index].tiltSpeed = stepper_tilt.maxSpeed();
    keyframe_array[current_keyframe_index].sliderSpeed = stepper_slider.maxSpeed();

    keyframe_array[current_keyframe_index].focusSpeed = stepper_focus.maxSpeed();
    keyframe_array[current_keyframe_index].zoomSpeed = stepper_zoom.maxSpeed();
    
    printi(F("Edited index: "), current_keyframe_index);
}

/*--------------------------------------------------------------------------------------------------------------------------------------------------------*/

void editDelay(unsigned int ms){
    keyframe_array[current_keyframe_index].msDelay = ms;
    printi(ms, F(""));
    printi(F("ms delay added at index: "), current_keyframe_index);
}

/*--------------------------------------------------------------------------------------------------------------------------------------------------------*/

void addDelay(unsigned int ms){
    addPosition();
    keyframe_array[current_keyframe_index].msDelay = ms;
    printi(ms, F(""));
    printi(F("ms delay added at index: "), current_keyframe_index);
}

/*--------------------------------------------------------------------------------------------------------------------------------------------------------*/

void invertPanDirection(bool invert){
    printi(F("Pan inversion: "), invert);
    invert_pan = invert;
    stepper_pan.setPinsInverted(invert, false, false);
}

/*--------------------------------------------------------------------------------------------------------------------------------------------------------*/

void invertTiltDirection(bool invert){
    printi(F("Tilt inversion: "), invert);
    invert_tilt = invert;
    stepper_tilt.setPinsInverted(invert, false, false);
}

/*--------------------------------------------------------------------------------------------------------------------------------------------------------*/

void invertSliderDirection(bool invert){
    printi(F("Slider inversion: "), invert);
    invert_slider = invert;
    stepper_slider.setPinsInverted(invert, false, false);
}

/*--------------------------------------------------------------------------------------------------------------------------------------------------------*/

void invertFocusDirection(bool invert){
    printi(F("Focus inversion: "), invert);
    invert_slider = invert;
    stepper_focus.setPinsInverted(invert, false, false);
}

/*--------------------------------------------------------------------------------------------------------------------------------------------------------*/


void invertZoomDirection(bool invert){
    printi(F("Zoom inversion: "), invert);
    invert_slider = invert;
    stepper_zoom.setPinsInverted(invert, false, false);
}

/*--------------------------------------------------------------------------------------------------------------------------------------------------------*/


void saveEEPROM(void){

  homing_mode_store.write(homing_mode);
  step_mode_store.write(step_mode);
  pan_max_speed_store.write(pan_max_speed);
  tilt_max_speed_store.write(tilt_max_speed);
  slider_max_speed_store.write(slider_max_speed);
  focus_max_speed_store.write(focus_max_speed);
  zoom_max_speed_store.write(zoom_max_speed);
  hall_pan_offset_degrees_store.write(hall_pan_offset_degrees);
  hall_tilt_offset_degrees_store.write(hall_tilt_offset_degrees);
  invert_pan_store.write(invert_pan);
  invert_tilt_store.write(invert_tilt);
  invert_slider_store.write(invert_slider);
  invert_focus_store.write(invert_focus);
  invert_zoom_store.write(invert_zoom);
  degrees_per_picture_store.write(degrees_per_picture);
  delay_ms_between_pictures_store.write(delay_ms_between_pictures);
  acceleration_enable_state_store.write(acceleration_enable_state);
  pan_accel_increment_us_store.write(pan_accel_increment_us);
  tilt_accel_increment_us_store.write(tilt_accel_increment_us);
  slider_accel_increment_us_store.write(slider_accel_increment_us);
  focus_accel_increment_us_store.write(focus_accel_increment_us);
  zoom_accel_increment_us_store.write(zoom_accel_increment_us);
}

/*--------------------------------------------------------------------------------------------------------------------------------------------------------*/

void printEEPROM(void){
    int itemp;
    float ftemp;
    itemp = step_mode_store.read();
    printi(F("FlashStorage:\nStep mode: "), itemp, F("\n"));

    ftemp = pan_max_speed_store.read();
    printi(F("Pan max: "), ftemp, 3, F("º/s\n"));

    ftemp = tilt_max_speed_store.read();
    printi(F("Tilt max: "), ftemp, 3, F("º/s\n"));
    
    ftemp = slider_max_speed_store.read();
    printi(F("Slider max: "), ftemp, 3, F("º/s\n"));

    ftemp = focus_max_speed_store.read();
    printi(F("Focus max: "), ftemp, 3, F("º/s\n"));

    ftemp = zoom_max_speed_store.read();
    printi(F("Zoom max: "), ftemp, 3, F("º/s\n"));

    ftemp = hall_pan_offset_degrees_store.read();
    printi(F("Pan offset: "), ftemp, 3, F("º/s\n"));

    ftemp = hall_tilt_offset_degrees_store.read();
    printi(F("Tilt offset: "), ftemp, 3, F("º/s\n"));

    ftemp = degrees_per_picture_store.read();
    printi(F("Angle between pics: "), ftemp, 3, F("º/s\n"));
    
    itemp = delay_ms_between_pictures_store.read();
    //printi(F("Delay between pics: "), itemp, 3, F("º/s\n"));
    
    printi(F("Pan invert: "), invert_pan_store.read());
   
    printi(F("Tilt invert: "), invert_tilt_store.read());
    
    printi(F("Slider invert: "), invert_slider_store.read());

    printi(F("Focus invert: "), invert_focus_store.read());
    printi(F("Zoom invert: "), invert_zoom_store.read());

    printi(F("Homing mode: "), homing_mode_store.read());

    printi(F("Accel enable: "), acceleration_enable_state_store.read());
    
    itemp = pan_accel_increment_us_store.read();
    printi(F("Pan accel delay: "), itemp, F("us\n"));

    itemp = tilt_accel_increment_us_store.read();
    printi(F("Tilt accel delay: "), itemp, F("us\n"));

    itemp = slider_accel_increment_us_store.read();
    printi(F("Slider accel delay: "), itemp, F("us\n"));
}

/*--------------------------------------------------------------------------------------------------------------------------------------------------------*/

void setEEPROMVariables(void){
    /*EEPROM.get(EEPROM_ADDRESS_MODE, step_mode);
    EEPROM.get(EEPROM_ADDRESS_PAN_MAX_SPEED, pan_max_speed);
    EEPROM.get(EEPROM_ADDRESS_TILT_MAX_SPEED, tilt_max_speed);
    EEPROM.get(EEPROM_ADDRESS_SLIDER_MAX_SPEED, slider_max_speed);

    EEPROM.get(EEPROM_ADDRESS_FOCUS_MAX_SPEED, focus_max_speed);
    EEPROM.get(EEPROM_ADDRESS_ZOOM_MAX_SPEED, zoom_max_speed);
    
    EEPROM.get(EEPROM_ADDRESS_HALL_PAN_OFFSET, hall_pan_offset_degrees);
    EEPROM.get(EEPROM_ADDRESS_HALL_TILT_OFFSET, hall_tilt_offset_degrees);
    EEPROM.get(EEPROM_ADDRESS_DEGREES_PER_PICTURE, degrees_per_picture);
    EEPROM.get(EEPROM_ADDRESS_PANORAMICLAPSE_DELAY, delay_ms_between_pictures);
    EEPROM.get(EEPROM_ADDRESS_PAN_ACCEL_INCREMENT_DELAY, pan_accel_increment_us);
    EEPROM.get(EEPROM_ADDRESS_TILT_ACCEL_INCREMENT_DELAY, tilt_accel_increment_us);
    EEPROM.get(EEPROM_ADDRESS_SLIDER_ACCEL_INCREMENT_DELAY, slider_accel_increment_us);        
    invert_pan = EEPROM.read(EEPROM_ADDRESS_INVERT_PAN);
    invert_tilt = EEPROM.read(EEPROM_ADDRESS_INVERT_TILT);
    invert_slider = EEPROM.read(EEPROM_ADDRESS_INVERT_SLIDER);

    invert_focus = EEPROM.read(EEPROM_ADDRESS_INVERT_FOCUS);
    invert_zoom = EEPROM.read(EEPROM_ADDRESS_INVERT_ZOOM);

    
    homing_mode = EEPROM.read(EEPROM_ADDRESS_HOMING_MODE);
    acceleration_enable_state = EEPROM.read(EEPROM_ADDRESS_ACCELERATION_ENABLE);*/
}

/*--------------------------------------------------------------------------------------------------------------------------------------------------------*/

void setHoming(byte homingType){
    if(homingType >= 0 && homingType <= 4){
        homing_mode = homingType;
        printi(F("Homing set to mode "), homingType, "\n");
    }
    else{
        printi(F("Invalid mode\n"));
    }
}

/*--------------------------------------------------------------------------------------------------------------------------------------------------------*/

void panoramiclapseInterpolation(float panStartAngle, float tiltStartAngle, float sliderStartPos, float panStopAngle, float tiltStopAngle, float sliderStopPos, float degPerPic, unsigned long msDelay){
    if(degPerPic == 0) return;
    if(msDelay > SHUTTER_DELAY){
        msDelay = msDelay - SHUTTER_DELAY;
    }
    float panAngle = panStopAngle - panStartAngle;
    float tiltAngle = tiltStopAngle - tiltStartAngle;
    float sliderDistance = sliderStopPos - sliderStartPos;
    float largestAngle = (abs(panAngle) > abs(tiltAngle)) ? panAngle : tiltAngle;
    unsigned int numberOfIncrements = abs(largestAngle) / degPerPic;
    if(numberOfIncrements == 0) return;
    float panInc = panAngle / numberOfIncrements;
    float tiltInc = tiltAngle / numberOfIncrements;
    float sliderInc = sliderDistance / numberOfIncrements;
    
    for(int i = 0; i <= numberOfIncrements; i++){
        setTargetPositions(panStartAngle + (panInc * i), tiltStartAngle + (tiltInc * i), sliderStartPos + (sliderInc * i),0,0);
        multi_stepper.runSpeedToPosition();//blocking move to the next position
        delay(msDelay / 2);
        triggerCameraShutter();//capture the picture
        delay(msDelay / 2);
    }
}

/*--------------------------------------------------------------------------------------------------------------------------------------------------------*/

void panoramiclapse(float degPerPic, unsigned long msDelay, int repeat){   
    if(keyframe_elements < 2){ 
        printi(F("Not enough keyframes\n"));
        return; //check there are posions to move to
    }
    for(int i = 0; i < repeat; i++){
        for(int index = 0; index < keyframe_elements - 1; index++){
            panoramiclapseInterpolation(panStepsToDegrees(keyframe_array[index].panStepCount), tiltStepsToDegrees(keyframe_array[index].tiltStepCount), sliderStepsToMillimetres(keyframe_array[index].sliderStepCount),
            panStepsToDegrees(keyframe_array[index + 1].panStepCount), tiltStepsToDegrees(keyframe_array[index + 1].tiltStepCount), sliderStepsToMillimetres(keyframe_array[index + 1].sliderStepCount), degPerPic, msDelay);
        }
    }
}

/*--------------------------------------------------------------------------------------------------------------------------------------------------------*/

void timelapse(unsigned int numberOfPictures, unsigned long msDelay){
    if(msDelay > SHUTTER_DELAY){
        msDelay = msDelay - SHUTTER_DELAY;
    }
    
    if(numberOfPictures > 1){
        numberOfPictures = numberOfPictures - 1;
    }
    
    unsigned long halfDelay = msDelay / 2;
   
    float panAngle = 0;
    float tiltAngle = 0;
    float sliderTravel = 0;
    
    if(keyframe_elements >= 2){ 
        panAngle = panStepsToDegrees(keyframe_array[1].panStepCount) - panStepsToDegrees(keyframe_array[0].panStepCount);
        tiltAngle = tiltStepsToDegrees(keyframe_array[1].tiltStepCount) - tiltStepsToDegrees(keyframe_array[0].tiltStepCount);
        sliderTravel = sliderStepsToMillimetres(keyframe_array[1].sliderStepCount) - sliderStepsToMillimetres(keyframe_array[0].sliderStepCount);
    }
    
    float sliderInc = sliderTravel / numberOfPictures;
    float panInc = panAngle / numberOfPictures;
    float tiltInc = tiltAngle / numberOfPictures;

    setTargetPositions(panStepsToDegrees(keyframe_array[0].panStepCount), tiltStepsToDegrees(keyframe_array[0].tiltStepCount), sliderStepsToMillimetres(keyframe_array[0].sliderStepCount),0,0);
    multi_stepper.runSpeedToPosition();//blocking move to the next position
    
    for(unsigned int i = 0; i <= numberOfPictures; i++){
        setTargetPositions(panStepsToDegrees(keyframe_array[0].panStepCount) + (panInc * i), tiltStepsToDegrees(keyframe_array[0].tiltStepCount) + (tiltInc * i), sliderStepsToMillimetres(keyframe_array[0].sliderStepCount) + (sliderInc * i),0,0);
        multi_stepper.runSpeedToPosition();//blocking move to the next position
        delay(halfDelay);
        triggerCameraShutter();//capture the picture
        delay(halfDelay);
    }
}

/*--------------------------------------------------------------------------------------------------------------------------------------------------------*/
//From the first two keyframes the intercept of where the camera is directed is calculated.
//The first kayframe's x pan and tilt positions are used to calculate a 3D vector. The second keyframe's x and pan position are used to calculate a vertical plane. (It wuld be almost impossible for 2 3D vectors to intercept due to floating point precision issues.)
//The intercept of the vectorand plane are then calculated to give the X, Y, Z coordinates of the point the camera was pointed at in both keyframes. (The second keyframe will ignore the tilt value and calculate it based on the first keyframes vector.)
bool calculateTargetCoordinate(void){ 
    float m1, c1, m2, c2;
    
    LinePoints line0;
    line0.x0 = sliderStepsToMillimetres(keyframe_array[0].sliderStepCount);
    line0.y0 = 0;
    line0.x1 = line0.x0 + cos(degToRads(panStepsToDegrees(keyframe_array[0].panStepCount)));
    line0.y1 = sin(degToRads(panStepsToDegrees(keyframe_array[0].panStepCount)));
    
    LinePoints line1;
    line1.x0 = sliderStepsToMillimetres(keyframe_array[1].sliderStepCount);
    line1.y0 = 0;
    line1.x1 = line1.x0 + cos(degToRads(panStepsToDegrees(keyframe_array[1].panStepCount)));
    line1.y1 = sin(degToRads(panStepsToDegrees(keyframe_array[1].panStepCount)));
    
    if((line0.x1 - line0.x0) != 0){
        m1 = (line0.y1 - line0.y0) / (line0.x1 - line0.x0);
        c1 = line0.y1 - m1 * line0.x1;
    }

    if((line1.x1 - line1.x0) != 0){
        m2 = (line1.y1 - line1.y0) / (line1.x1 - line1.x0);
        c2 = line1.y1 - m2 * line1.x1;
    }

    if((line0.x1 - line0.x0) == 0){
        intercept.x = line0.x0;
        intercept.y = m2 * intercept.x + c2;    
    }
    else if((line1.x1 - line1.x0) == 0){
        intercept.x = line1.x0;
        intercept.y = m1 * intercept.x + c1;
    }
    else{
        if(m1 == m2){ //If the angle of the slope of both lines are the same they are parallel and cannot intercept.
            printi(F("Positions do not intersect."));
            return false;
        }
        intercept.x = (c2 - c1) / (m1 - m2);
        intercept.y = m1 * intercept.x + c1;
    }
    intercept.z = tan(degToRads(tiltStepsToDegrees(keyframe_array[0].tiltStepCount))) * sqrt(pow(intercept.x - sliderStepsToMillimetres(keyframe_array[0].sliderStepCount), 2) + pow(intercept.y, 2));
    if(((panStepsToDegrees(keyframe_array[0].panStepCount) > 0 && panStepsToDegrees(keyframe_array[1].panStepCount) > 0) && intercept.y < 0)
    || ((panStepsToDegrees(keyframe_array[0].panStepCount) < 0 && panStepsToDegrees(keyframe_array[1].panStepCount) < 0) && intercept.y > 0) || intercept.y == 0){ //Checks that the intercept point is in the direction the camera was pointing and not on the opposite side behind the camera.
        printi(F("Invalid intercept.\n"));
        return false;
    }
    return true;
}

/*--------------------------------------------------------------------------------------------------------------------------------------------------------*/

void interpolateTargetPoint(FloatCoordinate targetPoint, int repeat){ //The first two keyframes are interpolated between while keeping the camera pointing at previously calculated intercept point.
    if(keyframe_elements < 2){ 
        printi(F("Not enough keyframes recorded\n"));
        return; //check there are posions to move to
    }

    float sliderStartPos = sliderStepsToMillimetres(keyframe_array[0].sliderStepCount); //slider start position
    float sliderEndPos = sliderStepsToMillimetres(keyframe_array[1].sliderStepCount);
    float panAngle = 0;
    float tiltAngle = 0;
    float x = targetPoint.x - sliderStepsToMillimetres(keyframe_array[0].sliderStepCount);
    float ySqared = pow(targetPoint.y, 2);    
    float sliderTravel = sliderStepsToMillimetres(keyframe_array[1].sliderStepCount) - sliderStepsToMillimetres(keyframe_array[0].sliderStepCount);
    int numberOfIncrements = abs(sliderTravel);
    float increment = sliderTravel / numberOfIncrements;//size of interpolation increments in mm
    
    for(int j = 0; (j < repeat || (repeat == 0 && j == 0)); j++){
        for(int i = 0; i <= numberOfIncrements; i++){
            x = targetPoint.x - (sliderStartPos + increment * i);
            panAngle = radsToDeg(atan2(targetPoint.y, x));
            tiltAngle = radsToDeg(atan2(targetPoint.z, sqrt(pow(x, 2) + ySqared)));
            setTargetPositions(panAngle, tiltAngle, sliderStartPos + increment * i,0,0);
            multi_stepper.runSpeedToPosition();//blocking move to the next position
        }
        x = targetPoint.x - sliderEndPos;
        panAngle = radsToDeg(atan2(targetPoint.y, x));
        tiltAngle = radsToDeg(atan2(targetPoint.z, sqrt(pow(x, 2) + ySqared)));
        setTargetPositions(panAngle, tiltAngle, sliderEndPos,0,0);
        multi_stepper.runSpeedToPosition();//blocking move to the next position

        for(int i = numberOfIncrements; (i >= 0 && repeat > 0); i--){
            x = targetPoint.x - (sliderStartPos + increment * i);
            panAngle = radsToDeg(atan2(targetPoint.y, x));
            tiltAngle = radsToDeg(atan2(targetPoint.z, sqrt(pow(x, 2) + ySqared)));
            setTargetPositions(panAngle, tiltAngle, sliderStartPos + increment * i,0,0);
            multi_stepper.runSpeedToPosition();//blocking move to the next position
        }
        if(repeat > 0){
            setTargetPositions(panAngle, tiltAngle, sliderStartPos,0,0);
            multi_stepper.runSpeedToPosition();//blocking move to the next position 
        }     
    }
}

/*--------------------------------------------------------------------------------------------------------------------------------------------------------*/

void toggleAcceleration(void){
    if(acceleration_enable_state == 0){
        acceleration_enable_state = 1;
        printi(F("Accel enabled.\n"));
    }
    else{
        acceleration_enable_state = 0;
        printi(F("Accel disabled.\n"));
    }
}

/*--------------------------------------------------------------------------------------------------------------------------------------------------------*/

void scaleKeyframeSpeed(float scaleFactor){
    if(scaleFactor <= 0){//Make sure a valid speed factor was entered
        printi(F("Invalid factor\n"));
        return; 
    }
    
    for(int row = 0; row < keyframe_elements; row++){
        keyframe_array[row].panSpeed *= scaleFactor;
        keyframe_array[row].tiltSpeed *= scaleFactor;
        keyframe_array[row].sliderSpeed *= scaleFactor;
    }
    printi(F("Keyframe speed scaled by "), scaleFactor, 3, F("\n"));
}

/*--------------------------------------------------------------------------------------------------------------------------------------------------------*/

void serialData(void){
  //char stringText[MAX_STRING_LENGTH + 1];
    char instruction = Serial.read();
    if(instruction == INSTRUCTION_BYTES_SLIDER_PAN_TILT_SPEED){
        int count = 0;
        while(Serial.available() < 10){//Wait for 6 bytes to be available. Breaks after ~20ms if bytes are not received.
                delayMicroseconds(200); 
                count++;
                if(count > 100){
                    serialFlush();//Clear the serial buffer
                    break;
                }
            }
            int16_t sliderStepSpeed = (Serial.read() << 8) + Serial.read(); 
            int16_t panStepSpeed = (Serial.read() << 8) + Serial.read(); 
            int16_t tiltStepSpeed = (Serial.read() << 8) + Serial.read();
            int16_t focusStepSpeed = (Serial.read() << 8) + Serial.read();
            int16_t zoomStepSpeed = (Serial.read() << 8) + Serial.read();
            
            stepper_slider.setSpeed(sliderStepSpeed);
            stepper_pan.setSpeed(panStepSpeed);
            stepper_tilt.setSpeed(tiltStepSpeed);
            stepper_focus.setSpeed(focusStepSpeed);
            stepper_zoom.setSpeed(zoomStepSpeed);

            stepper_slider.runSpeed();
            stepper_pan.runSpeed();
            stepper_tilt.runSpeed();
            stepper_focus.runSpeed();
            stepper_zoom.runSpeed();
    }
    
    delay(2); //wait to make sure all data in the serial message has arived 
    memset(&stringText[0], 0, sizeof(stringText)); //clear the array
    while(Serial.available()){//set elemetns of stringText to the serial values sent
        char digit = Serial.read(); //read in a char
        strncat(stringText, &digit, 1); //add digit to the end of the array
    }
    serialFlush();//Clear any excess data in the serial buffer
    int serialCommandValueInt = atoi(stringText); //converts stringText to an int
    float serialCommandValueFloat = atof(stringText); //converts stringText to a float
    if(instruction == '+'){//The Bluetooth module sends a message starting with "+CONNECTING" which should be discarded.
        delay(100); //wait to make sure all data in the serial message has arived 
        serialFlush();//Clear any excess data in the serial buffer
        return;
    }
    switch(instruction){        
        case INSTRUCTION_SCALE_SPEED:{
            scaleKeyframeSpeed(serialCommandValueFloat);
        }
        break;
        case INSTRUCTION_PAN_ACCEL_INCREMENT_DELAY:{
            pan_accel_increment_us = (serialCommandValueInt >= 0) ? serialCommandValueInt : 0;
            printi(F("Pan accel delay: "), pan_accel_increment_us, F("us\n"));
        }
        break;
        case INSTRUCTION_TILT_ACCEL_INCREMENT_DELAY:{
            tilt_accel_increment_us = (serialCommandValueInt >= 0) ? serialCommandValueInt : 0;
            printi(F("Tilt accel delay: "), tilt_accel_increment_us, F("us\n"));
        }
        break;
        case INSTRUCTION_SLIDER_ACCEL_INCREMENT_DELAY:{
            slider_accel_increment_us = (serialCommandValueInt >= 0) ? serialCommandValueInt : 0;
            printi(F("Slider accel delay: "), slider_accel_increment_us, F("us\n"));
        }
        break;
        case INSTRUCTION_ACCEL_ENABLE:{
            toggleAcceleration();
        }
        break;
        case INSTRUCTION_SLIDER_MILLIMETRES:{
            sliderMoveTo(serialCommandValueFloat);
        }
        break;
        case INSTRUCTION_TIMELAPSE:{
            printi(F("Timelapse with "), serialCommandValueInt, F(" pics\n"));
            printi(F("Finished\n"));
        }
        break;
        case INSTRUCTION_AUTO_HOME:{
            printi(F("Homing\n"));
            if(findHome()){
                printi(F("Complete\n"));
            }
            else{
                stepper_pan.setCurrentPosition(0);
                stepper_tilt.setCurrentPosition(0);
                stepper_slider.setCurrentPosition(0);
                
                stepper_focus.setCurrentPosition(0);
                stepper_zoom.setCurrentPosition(0);
                
                setTargetPositions(0, 0, 0,0,0);
                printi(F("Error homing\n"));
            }
        }
        break;
        case INSTRUCTION_SET_HOMING:{
            setHoming(serialCommandValueInt);
        }
        break;
        case INSTRUCTION_SET_PAN_HALL_OFFSET:{
            hall_pan_offset_degrees = serialCommandValueFloat;
            printi(F("Pan offset: "), hall_pan_offset_degrees, 3, F("º\n"));
        }
        break;
        case INSTRUCTION_SET_TILT_HALL_OFFSET:{
            hall_tilt_offset_degrees = serialCommandValueFloat;
            printi(F("Tilt offset: "), hall_tilt_offset_degrees, 3, F("º\n"));
        }
        break;
         case INSTRUCTION_INVERT_SLIDER:{
            invertSliderDirection(serialCommandValueInt);
        }
        break;
        case INSTRUCTION_INVERT_TILT:{
            invertTiltDirection(serialCommandValueInt);
        }
        break;
        case INSTRUCTION_INVERT_PAN:{
            invertPanDirection(serialCommandValueInt);
        }
        break;
        case INSTRUCTION_INVERT_FOCUS:{
            invertFocusDirection(serialCommandValueInt);
        }
        break;
        case INSTRUCTION_INVERT_ZOOM:{
            invertZoomDirection(serialCommandValueInt);
        }
        break;
        case INSTRUCTION_SAVE_TO_FLASHSTORAGE:{
            saveEEPROM();
            printi(F("Saved to FlashStorage\n"));
        }
        break;
        case INSTRUCTION_ADD_POSITION:{
            addPosition();
        }
        break;
        case INSTRUCTION_STEP_FORWARD:{
            moveToIndex(current_keyframe_index + 1);
            printi(F("Index: "), current_keyframe_index, F("\n"));
        }
        break;
        case INSTRUCTION_STEP_BACKWARD:{
            moveToIndex(current_keyframe_index - 1);
            printi(F("Index: "), current_keyframe_index, F("\n"));
        }
        break;
        case INSTRUCTION_JUMP_TO_START:{
            gotoFirstKeyframe();
            printi(F("Index: "), current_keyframe_index, F("\n"));
        }
        break;
        case INSTRUCTION_JUMP_TO_END:{
            gotoLastKeyframe();
            printi(F("Index: "), current_keyframe_index, F("\n"));
        }
        break;
        case INSTRUCTION_EDIT_ARRAY:{
            editKeyframe();
        }
        break;
        case INSTRUCTION_ADD_DELAY:{
            addDelay(serialCommandValueInt);
        }
        break;
        case INSTRUCTION_EDIT_DELAY:{
            editDelay(serialCommandValueInt);
        }
        break;
        case INSTRUCTION_CLEAR_ARRAY:{
            clearKeyframes();
        }
        break;
        case INSTRUCTION_EXECUTE_MOVES:{
            executeMoves(serialCommandValueInt);
        }
        break;      
        case INSTRUCTION_DEBUG_STATUS:{
            debugReport();
        }
        break;
        case INSTRUCTION_PAN_DEGREES:{
            panDegrees(serialCommandValueFloat);
        }
        break;  
        case INSTRUCTION_TILT_DEGREES:{
            tiltDegrees(serialCommandValueFloat);
        }
        break; 
        case INSTRUCTION_FOCUS_DEGREES:{
            focusDegrees(serialCommandValueFloat);
        }
        break;  
        case INSTRUCTION_ZOOM_DEGREES:{
            zoomDegrees(serialCommandValueFloat);
        }
        break;  
        case INSTRUCTION_ENABLE:{
            enableSteppers();
        }
        break; 
        case INSTRUCTION_STEP_MODE:{
            setStepMode(serialCommandValueInt);
        }
        break; 
        case INSTRUCTION_SET_PAN_SPEED:{
            printi(F("Max pan speed: "), serialCommandValueFloat, 1, "deg/s.\n");
            pan_max_speed = serialCommandValueFloat;
            stepper_pan.setMaxSpeed(panDegreesToSteps(pan_max_speed));
        }
        break; 
        case INSTRUCTION_SET_TILT_SPEED:{
            printi(F("Max tilt speed: "), serialCommandValueFloat, 1, "deg/s.\n");
            tilt_max_speed = serialCommandValueFloat;
            stepper_tilt.setMaxSpeed(tiltDegreesToSteps(tilt_max_speed));
        }
        break;
        case INSTRUCTION_SET_SLIDER_SPEED:{
            printi(F("Max slider speed: "), serialCommandValueFloat, 1, "mm/s.\n");
            slider_max_speed = serialCommandValueFloat;
            stepper_slider.setMaxSpeed(sliderMillimetresToSteps(slider_max_speed));
        }
        break;
        case INSTRUCTION_CALCULATE_TARGET_POINT:{            
            if(calculateTargetCoordinate()){
                printi("Target:\tx: ", intercept.x, 3, "\t");
                printi("y: ", intercept.y, 3, "\t");
                printi("z: ", intercept.z, 3, "mm\n");
            }
        }
        break;  
        case INSTRUCTION_ORIBIT_POINT:{            
            if(calculateTargetCoordinate()){
                interpolateTargetPoint(intercept, serialCommandValueInt);
            }
        }
        break;
    }
}

/*--------------------------------------------------------------------------------------------------------------------------------------------------------*/

void mainLoop(void){
    while(1){
        if(Serial.available()) serialData();
        multi_stepper.run();
    }
}

/*--------------------------------------------------------------------------------------------------------------------------------------------------------*/
